Nadoooor/SnakeHome/Photos/Journal/snakeface.jpg

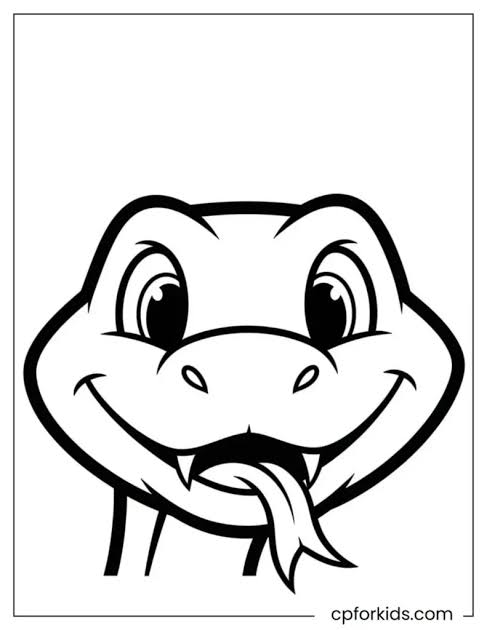
Photos/Journal/snakeface.jpg
